tysovsky/ampsim/Photos/IMG_1066.jpeg

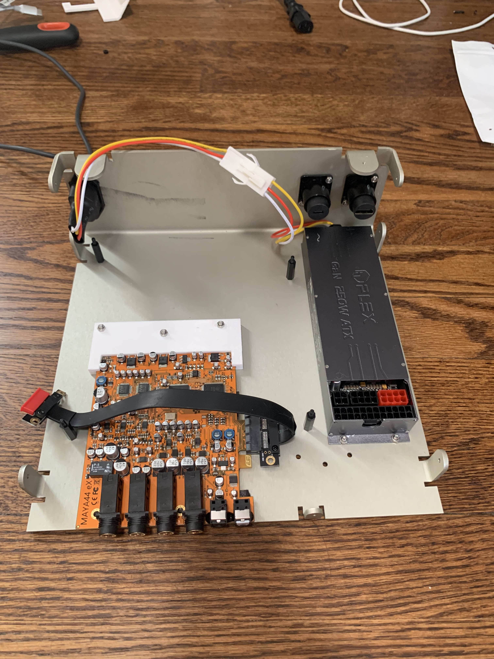
Photos/IMG_1066.jpeg
