tysovsky/ampsim/Photos/IMG_1067.jpeg

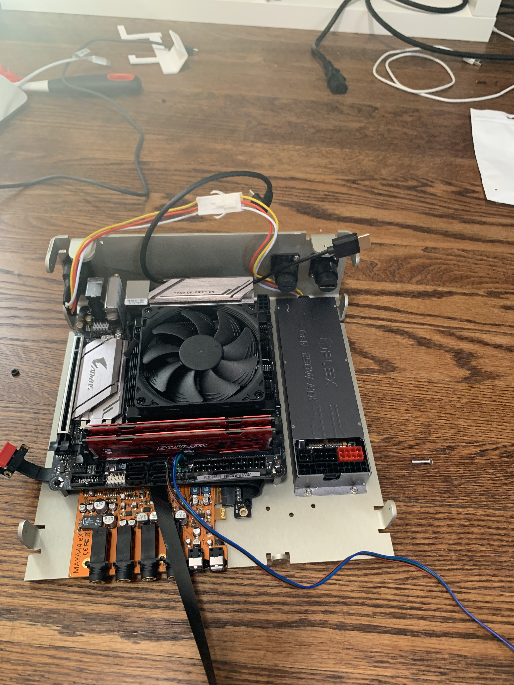
Photos/IMG_1067.jpeg
