tysovsky/ampsim/Photos/IMG_1071.jpeg

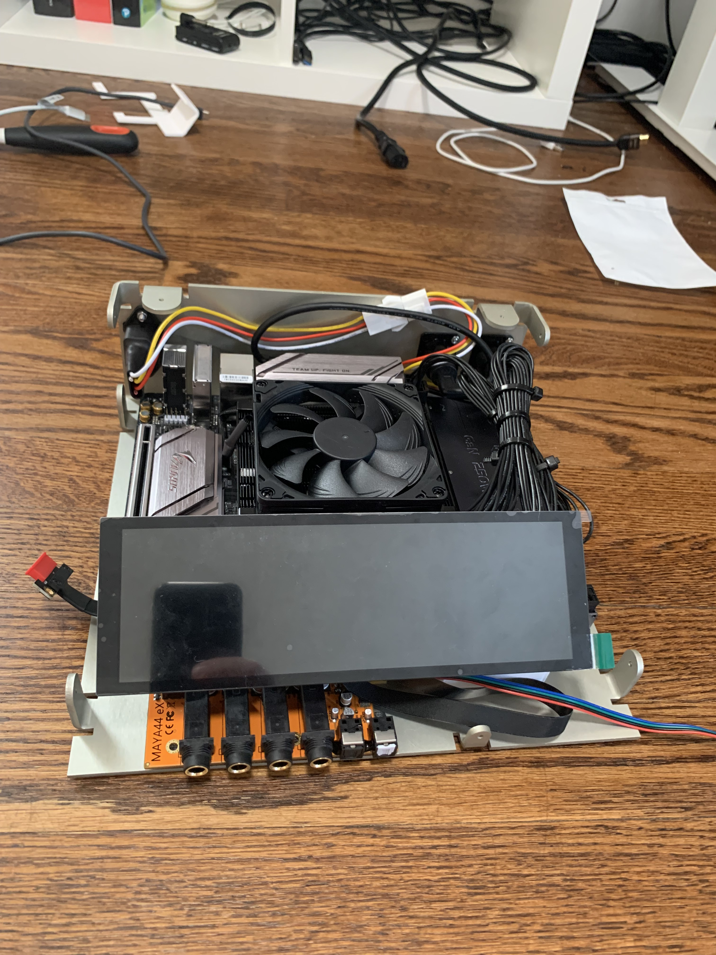
Photos/IMG_1071.jpeg
