tysovsky/ampsim/Photos/IMG_1097.jpeg

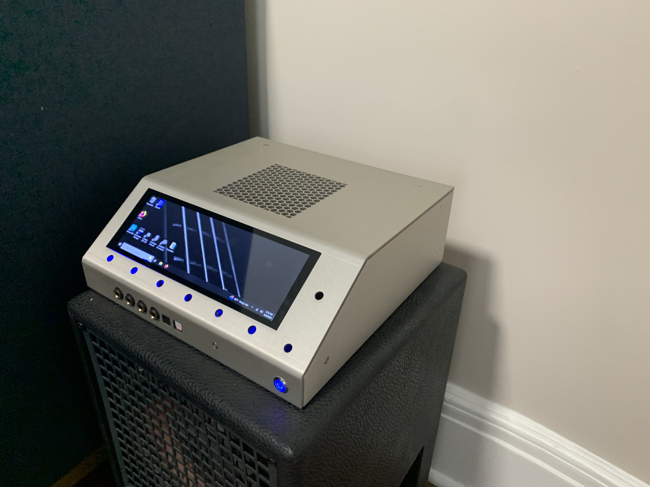
Photos/IMG_1097.jpeg
