tysovsky/ampsim/Photos/IMG_1064.jpeg

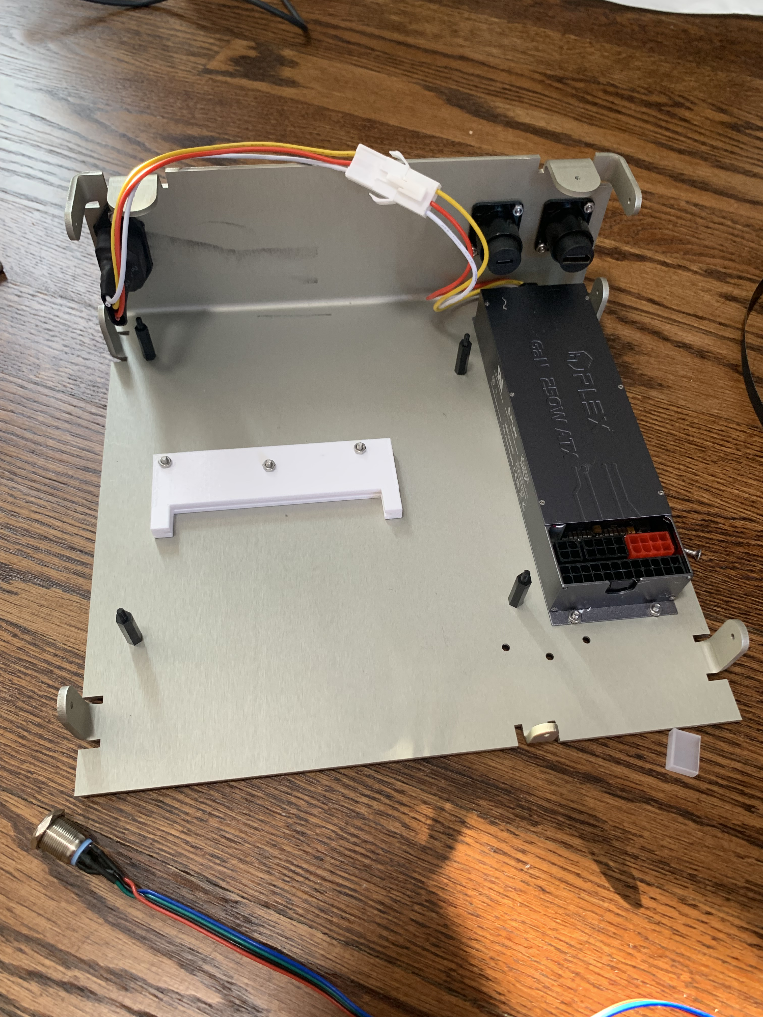
Photos/IMG_1064.jpeg
