tysovsky/ampsim/Photos/IMG_1065.jpeg

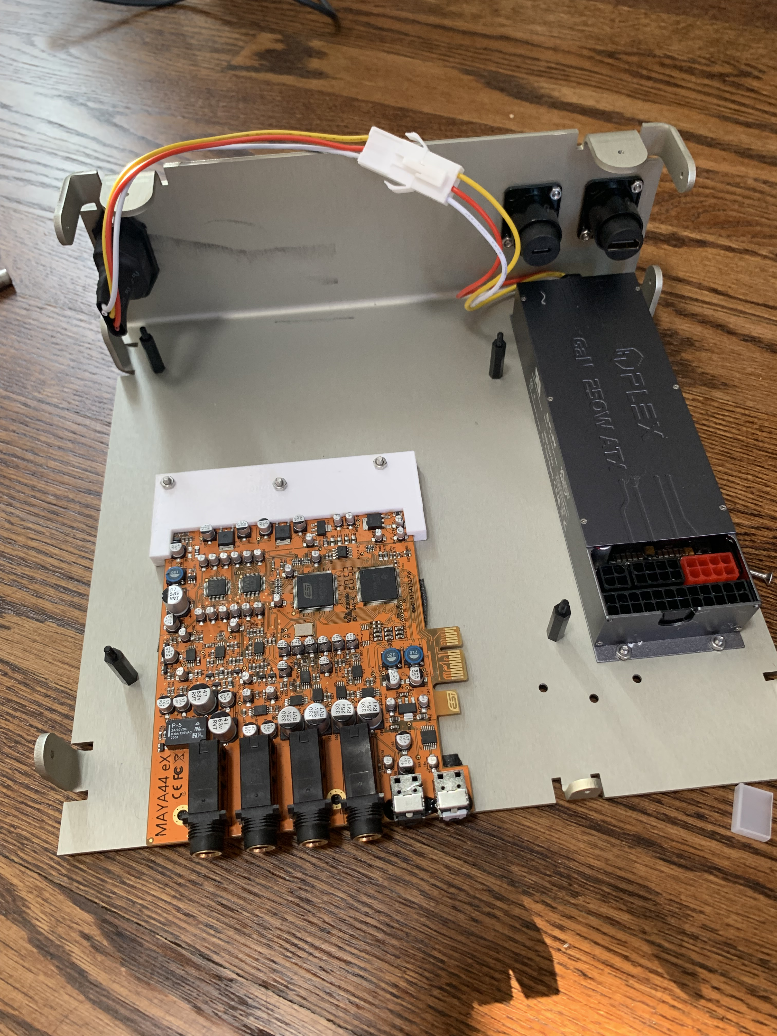
Photos/IMG_1065.jpeg
