tysovsky/ampsim/Photos/IMG_1069.jpeg

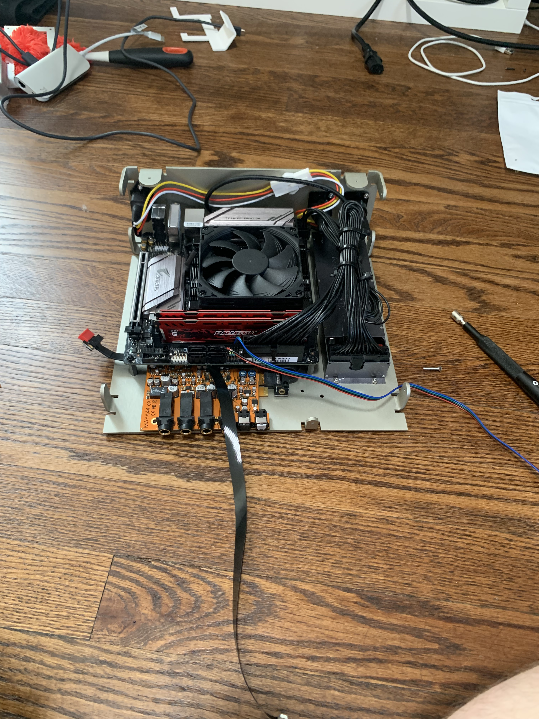
Photos/IMG_1069.jpeg
