tysovsky/ampsim/Photos/IMG_1070.jpeg

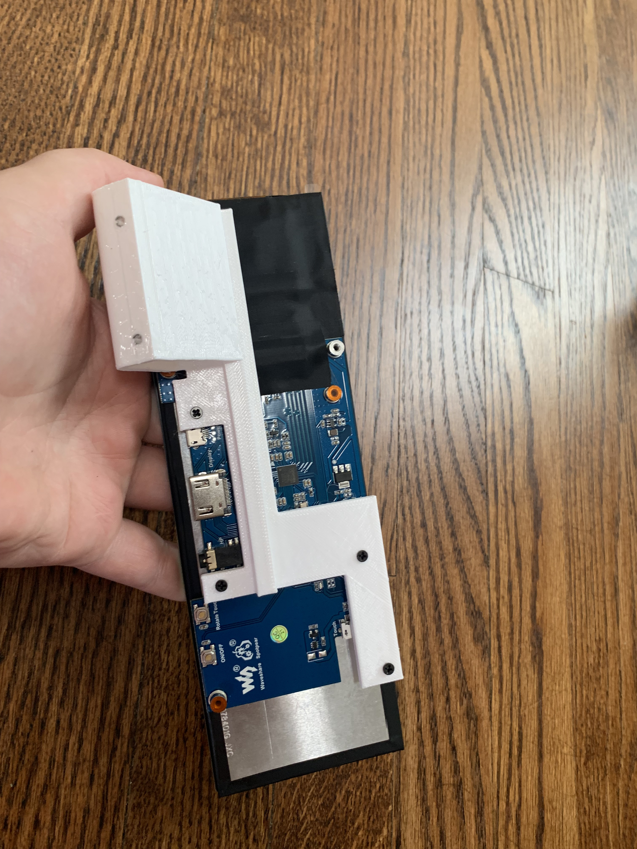
Photos/IMG_1070.jpeg
